jbilander/SDBox-v2/images/SDBox-v2_case_cura_slicing.jpg

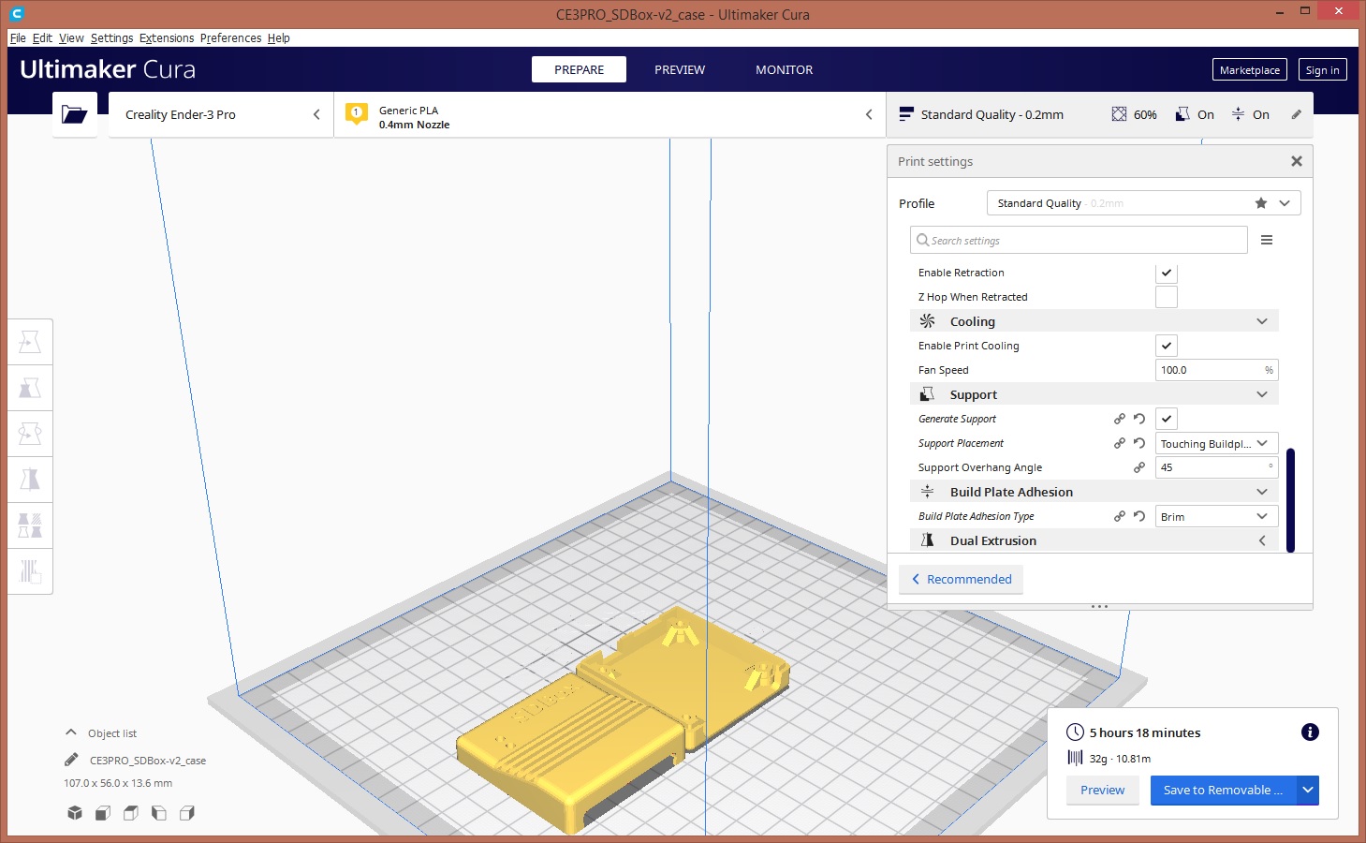
images/SDBox-v2_case_cura_slicing.jpg
