jbilander/SDBox-v2/images/SDBox-v2_pic8.jpg

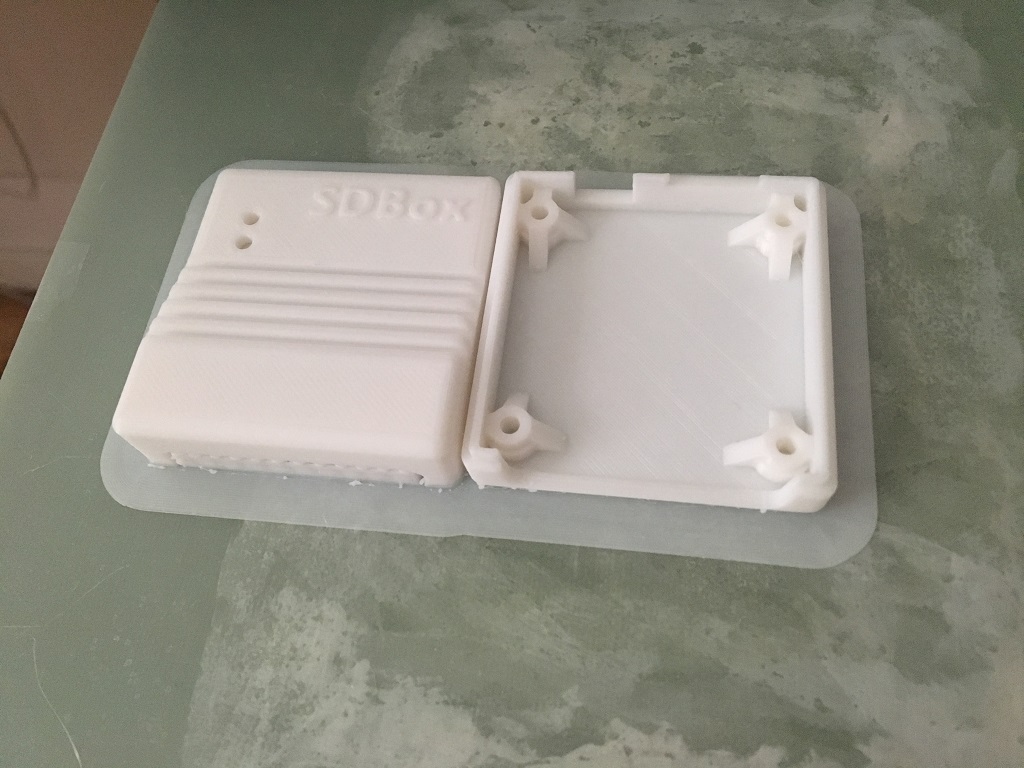
images/SDBox-v2_pic8.jpg
