jbilander/SDBox-v2/images/SDBox-v2_text.jpg

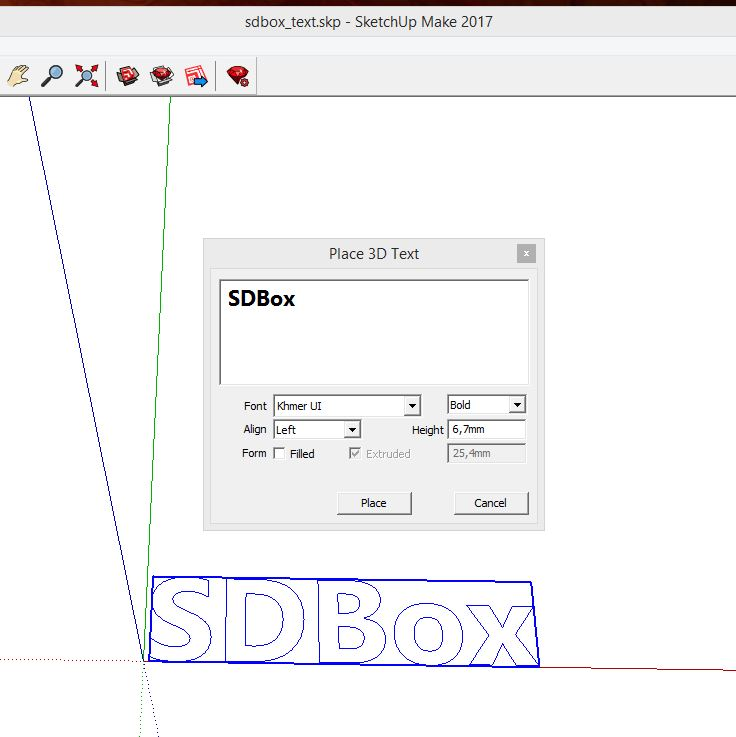
images/SDBox-v2_text.jpg
